Sn3akySqu1d/Squidboard/Images/image-20.png

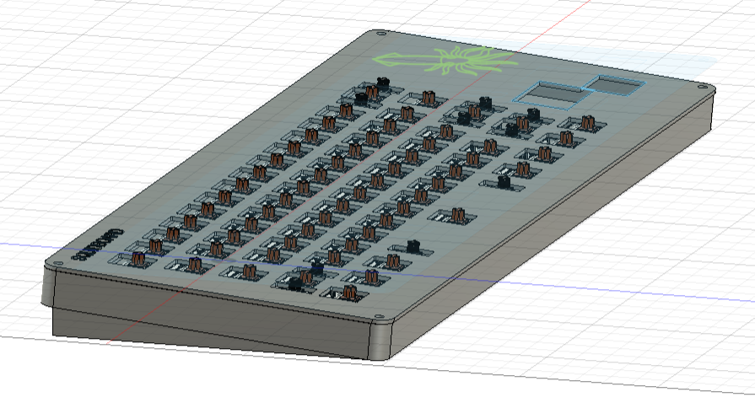
Images/image-20.png
