Sn3akySqu1d/Squidboard/Images/image.png

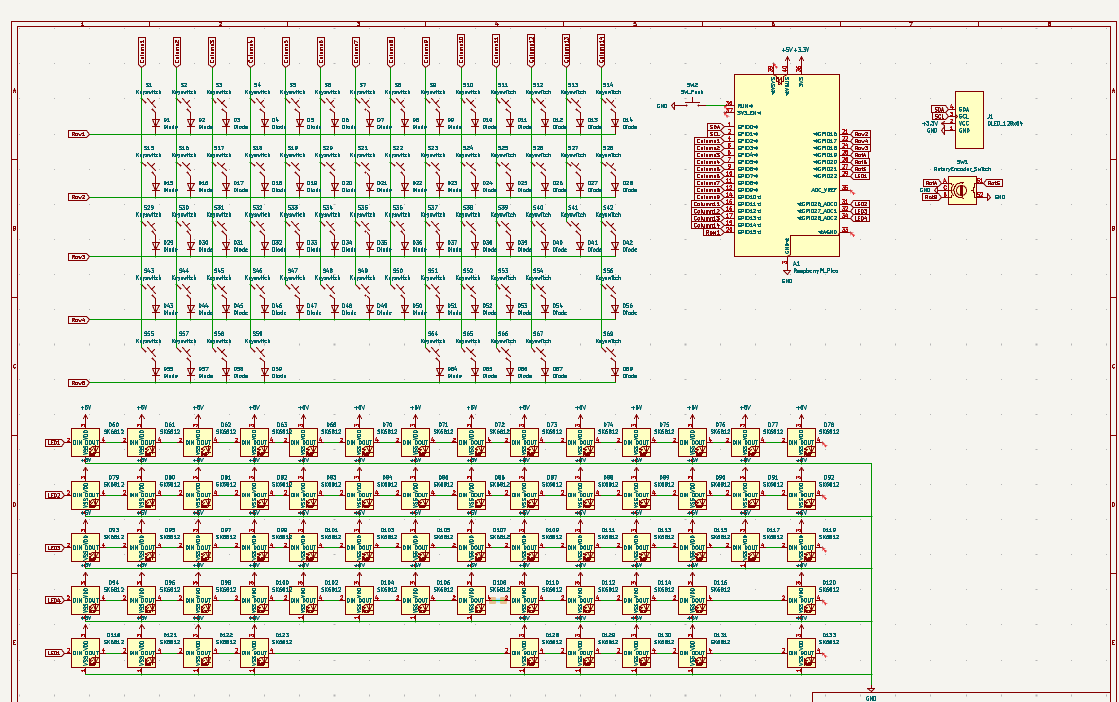
Images/image.png
