Sn3akySqu1d/Squidboard/JournalImages/image-1.png

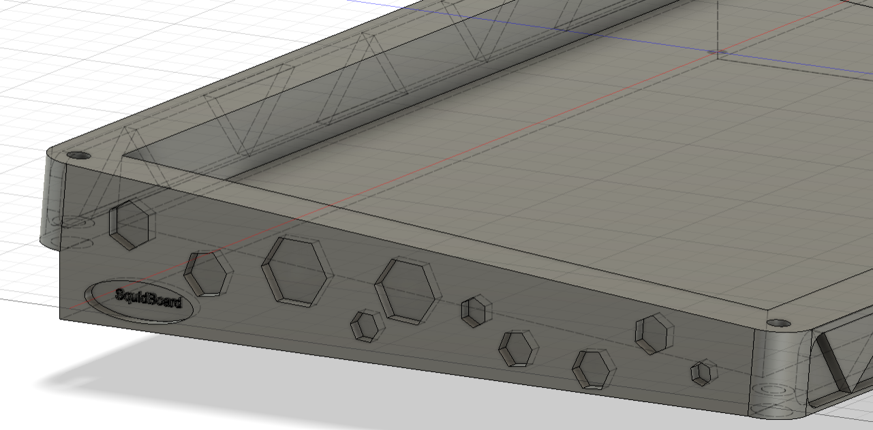
JournalImages/image-1.png
