Sn3akySqu1d/Squidboard/JournalImages/image-2.png

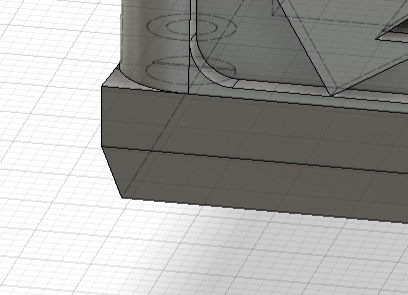
JournalImages/image-2.png
