Sn3akySqu1d/Squidboard/JournalImages/image-3.png

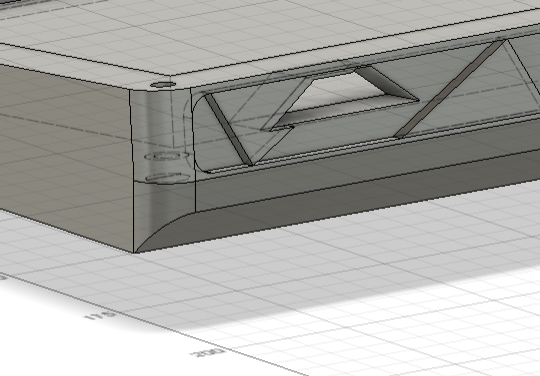
JournalImages/image-3.png
