Sn3akySqu1d/Squidboard/JournalImages/image-5.png

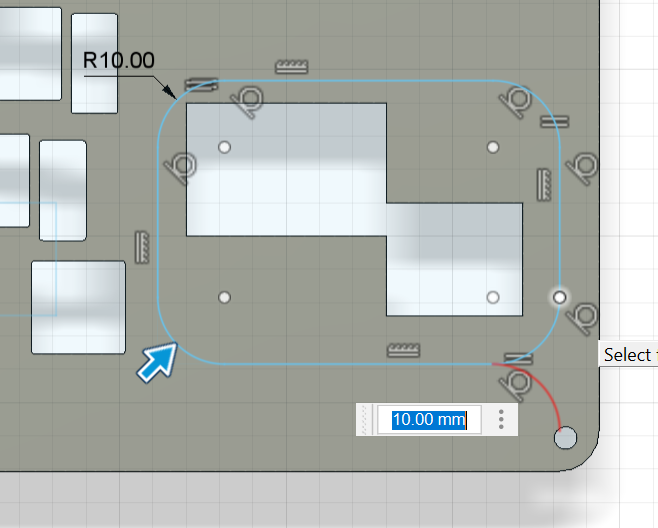
JournalImages/image-5.png
