Sn3akySqu1d/Squidboard/JournalImages/image-6.png

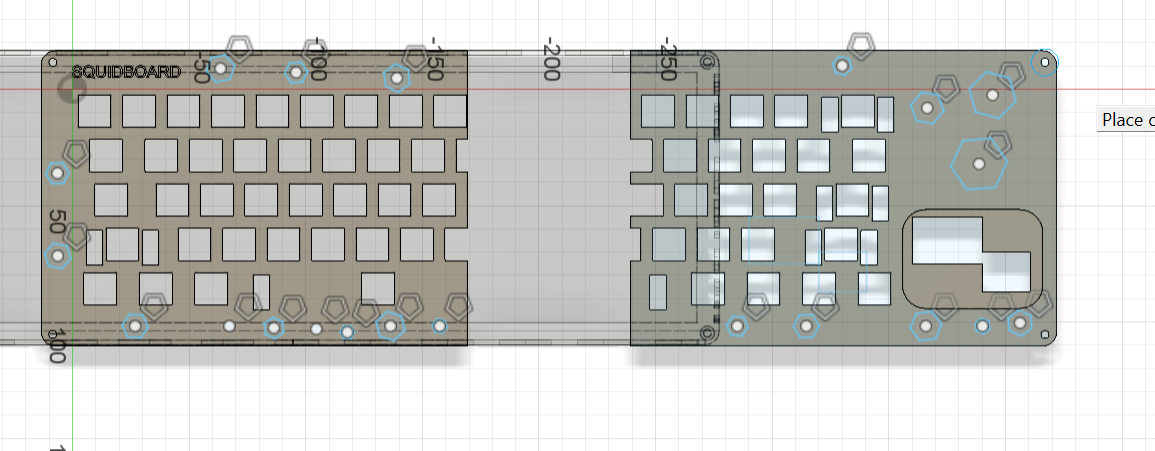
JournalImages/image-6.png
