Sn3akySqu1d/Squidboard/JournalImages/image-7.png

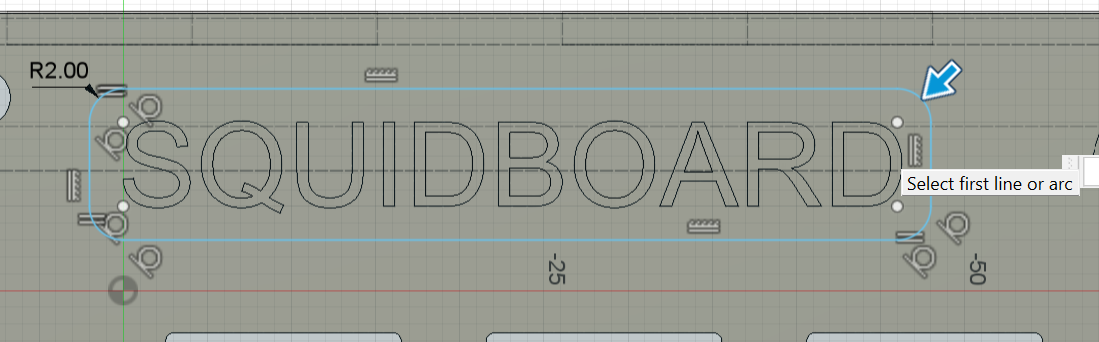
JournalImages/image-7.png
