Sn3akySqu1d/Squidboard/JournalImages/image-8.png

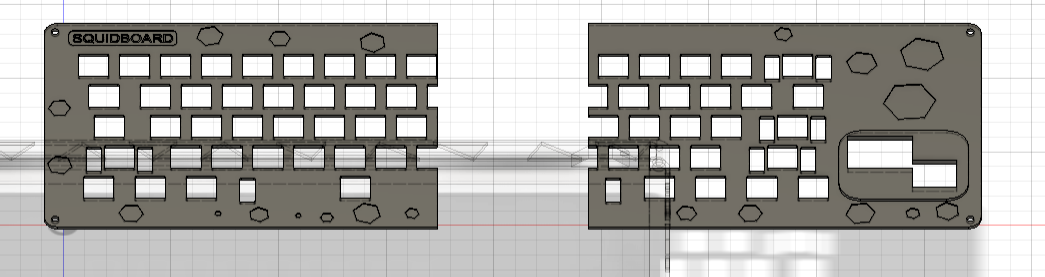
JournalImages/image-8.png
