Sn3akySqu1d/Squidboard/JournalImages/image-9.png

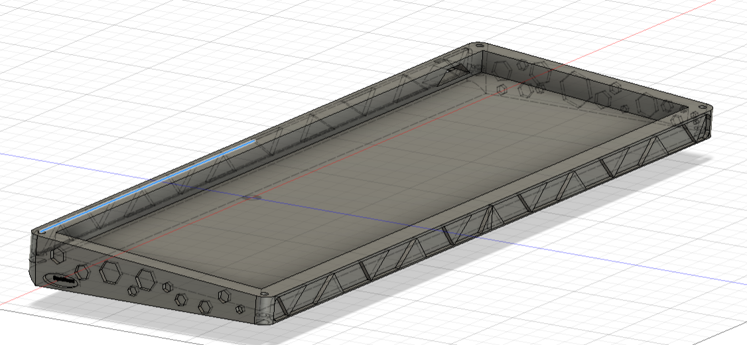
JournalImages/image-9.png
