Sn3akySqu1d/Squidboard/JournalImages/image-10.png

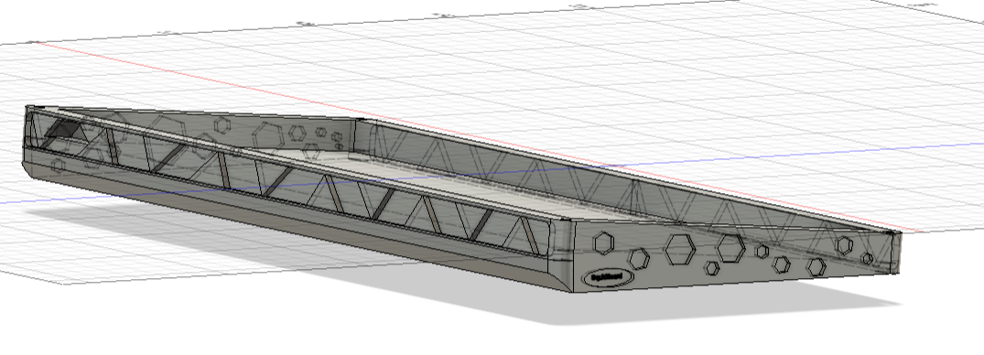
JournalImages/image-10.png
