Sn3akySqu1d/Squidboard/JournalImages/image-11.png

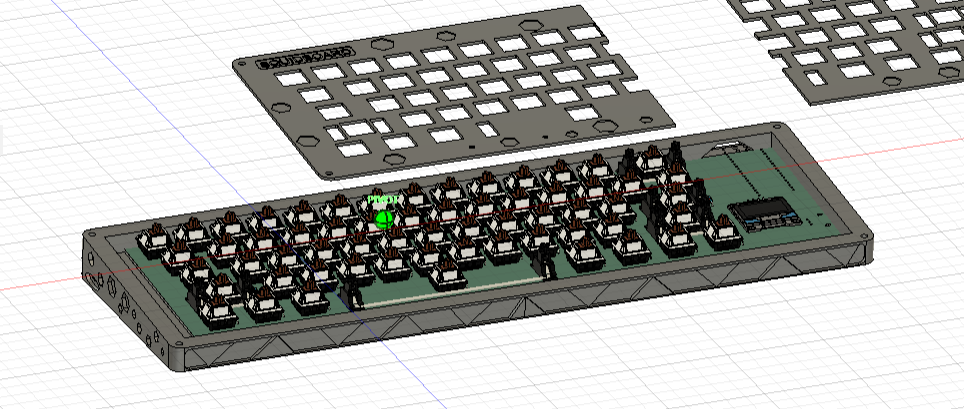
JournalImages/image-11.png
