Sn3akySqu1d/Squidboard/JournalImages/image-15.png

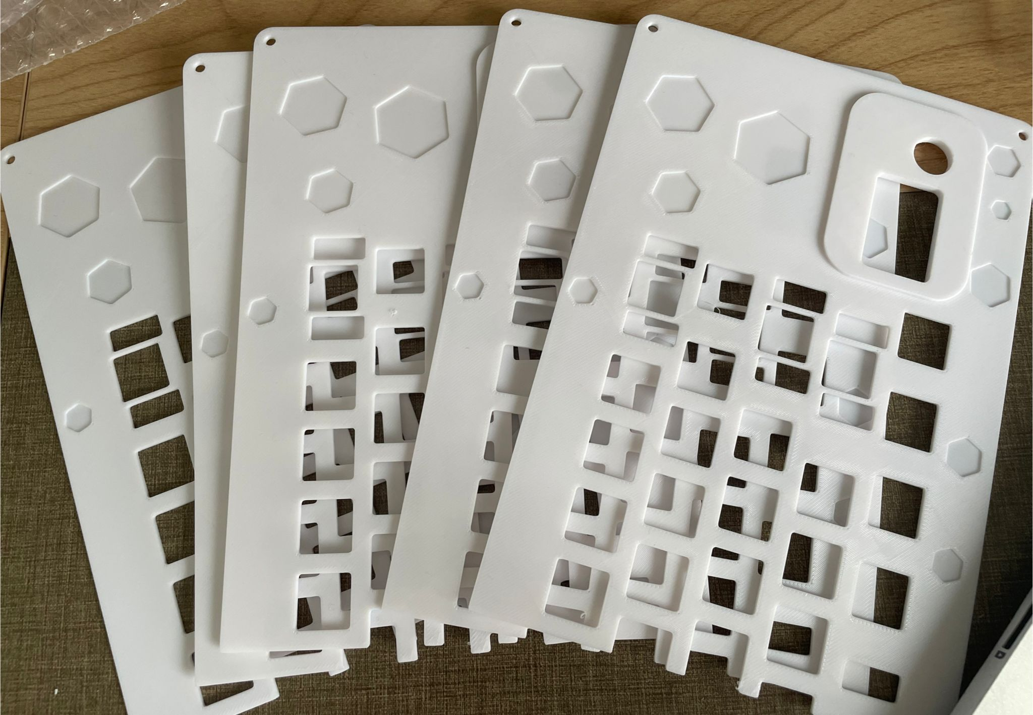
JournalImages/image-15.png
