Sn3akySqu1d/Squidboard/JournalImages/image-16.png

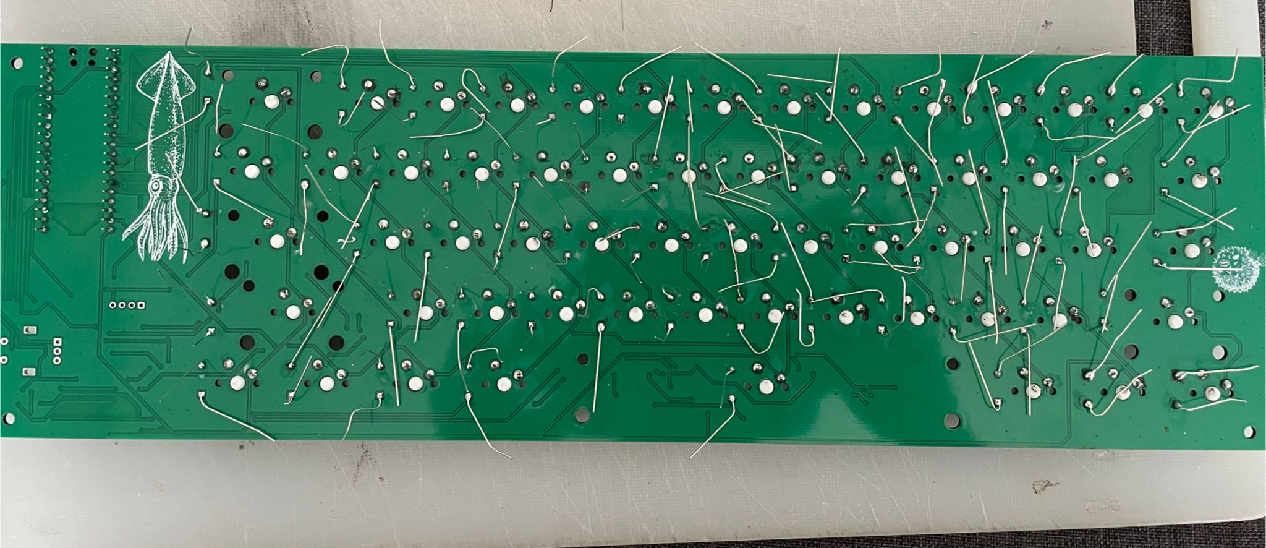
JournalImages/image-16.png
