Sn3akySqu1d/Squidboard/JournalImages/image-17.png

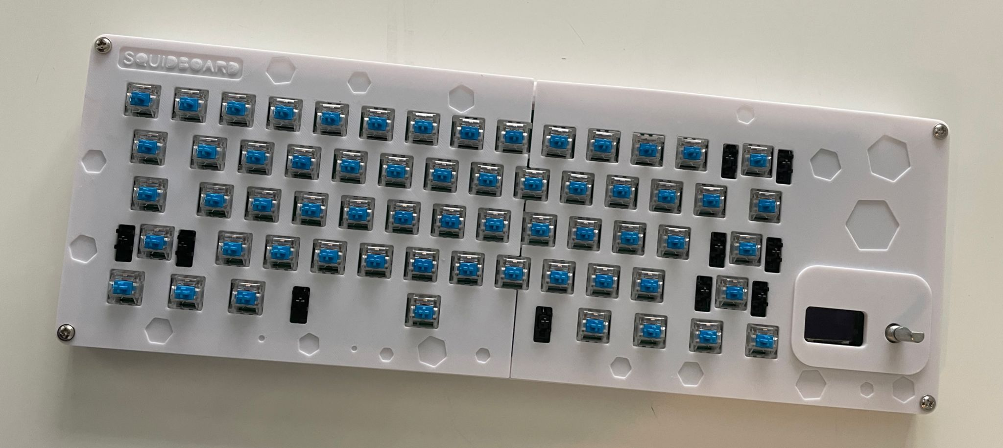
JournalImages/image-17.png
