Sn3akySqu1d/Squidboard/JournalImages/image-19.png

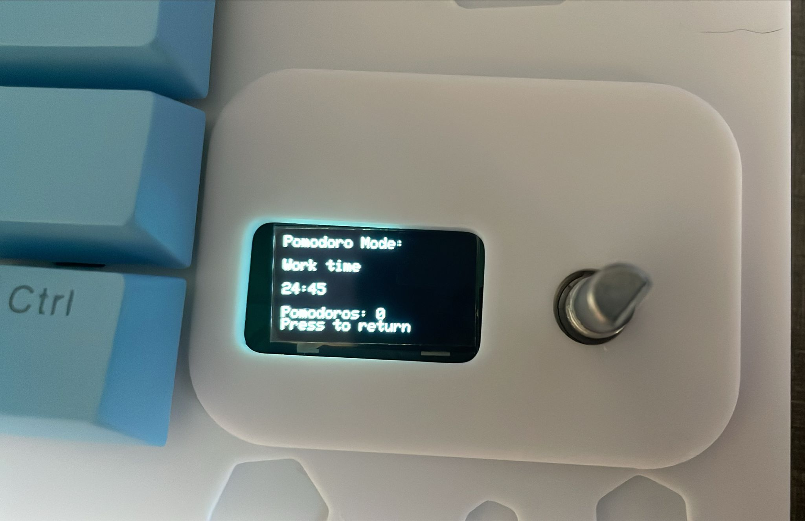
JournalImages/image-19.png
