Sn3akySqu1d/Squidboard/JournalImages/image.png

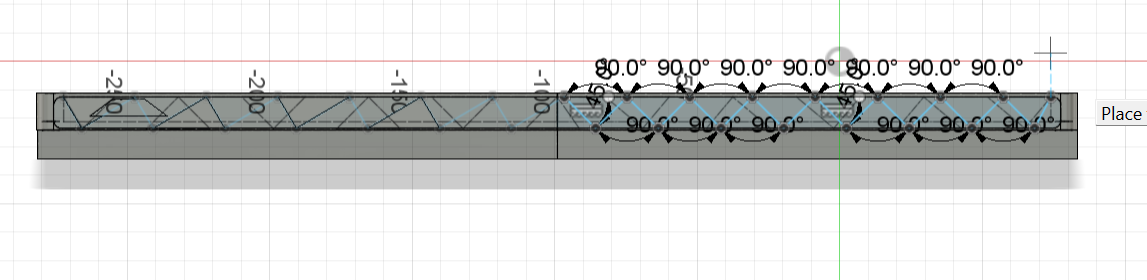
JournalImages/image.png
