Sn3akySqu1d/Squidboard/Kicad/Mechboard/Mechboard.kicad_sch

## KiCad design Kicad/Mechboard/Mechboard.kicad_sch (2025-07-20)

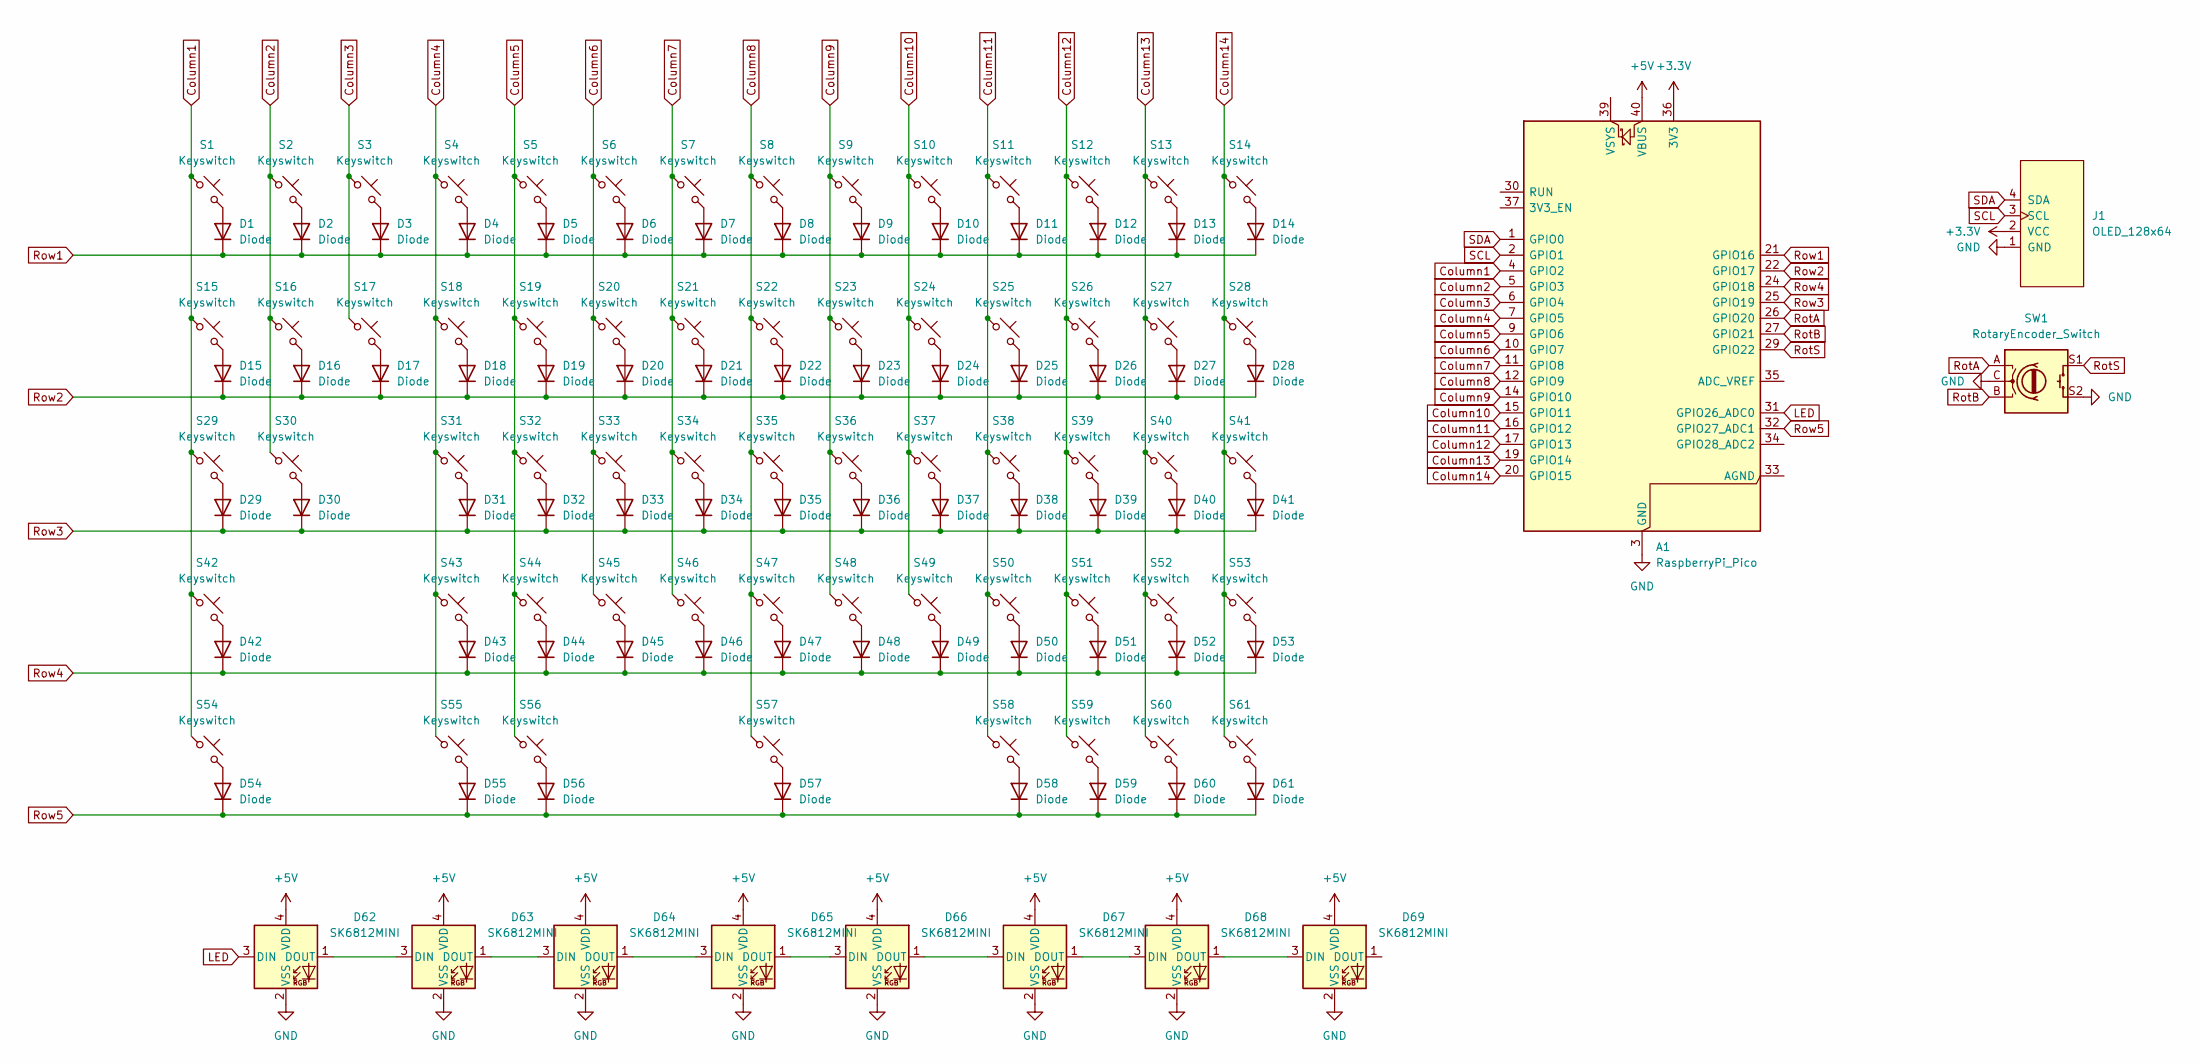
[picture p31: schematic Mechboard.kicad_sch]

Parts:
A1: RaspberryPi_Pico; RaspberryPi_Pico_Common_Unspecified
D1, D2, D3, D4, D5, D6, D7, D8, D9, D10, D11, D12, D13, D14, D15, D16, D17, D18, D19, D20, D21, D22, D23, D24, D25, D26, D27, D28, D29, D30, D31, D32, D33, D34, D35, D36, D37, D38, D39, D40, D41, D42, D43, D44, D45, D46, D47, D48, D49, D50, D51, D52, D53, D54, D55, D56, D57, D58, D59, D60, D61: Diode; Diode_DO-35
D62, D63, D64, D65, D66, D67, D68, D69: SK6812MINI; LED_SK6812MINI_PLCC4_3.5x3.5mm_P1.75mm
J1: OLED_128x64
S1, S2, S3, S4, S5, S6, S7, S8, S9, S10, S11, S12, S13, S16, S17, S18, S19, S20, S21, S22, S23, S24, S25, S26, S27, S30, S31, S32, S33, S34, S35, S36, S37, S38, S39, S40, S43, S44, S45, S46, S47, S48, S49, S50, S51, S52: Keyswitch; MX_PCB_1.00u
S14: Keyswitch; MX_PCB_2.00u
S15, S28: Keyswitch; MX_PCB_1.50u
S29: Keyswitch; MX_PCB_1.75u
S41, S42: Keyswitch; MX_PCB_2.25u
S53: Keyswitch; MX_PCB_2.75u
S54, S55, S56, S58, S59, S60, S61: Keyswitch; MX_PCB_1.25u
S57: Keyswitch; MX_PCB_6.25u
SW1: RotaryEncoder_Switch; RotaryEncoder_Alps_EC11E-Switch_Vertical_H20mm

Connections:
+3.3V: A1.36 (3V3), J1.2 (VCC)
+5V: A1.40 (VBUS), D62.4 (VDD), D63.4 (VDD), D64.4 (VDD), D65.4 (VDD), D66.4 (VDD), D67.4 (VDD), D68.4 (VDD), D69.4 (VDD)
Column1: A1.4 (GPIO2), S1.1, S15.1, S29.1, S42.1, S54.1
Column2: A1.5 (GPIO3), S2.1, S16.1, S30.1
Column3: A1.6 (GPIO4), S3.1, S17.1
Column4: A1.7 (GPIO5), S4.1, S18.1, S31.1, S43.1, S55.1
Column5: A1.9 (GPIO6), S5.1, S19.1, S32.1, S44.1, S56.1
Column6: A1.10 (GPIO7), S6.1, S20.1, S33.1, S45.1
Column7: A1.11 (GPIO8), S7.1, S21.1, S34.1, S46.1
Column8: A1.12 (GPIO9), S8.1, S22.1, S35.1, S47.1, S57.1
Column9: A1.14 (GPIO10), S9.1, S23.1, S36.1, S48.1
Column10: A1.15 (GPIO11), S10.1, S24.1, S37.1, S49.1
Column11: A1.16 (GPIO12), S11.1, S25.1, S38.1, S50.1, S58.1
Column12: A1.17 (GPIO13), S12.1, S26.1, S39.1, S51.1, S59.1
Column13: A1.19 (GPIO14), S13.1, S27.1, S40.1, S52.1, S60.1
Column14: A1.20 (GPIO15), S14.1, S28.1, S41.1, S53.1, S61.1
GND: A1.3 (GND), A1.8 (GND), A1.13 (GND), A1.18 (GND), A1.23 (GND), A1.28 (GND), A1.38 (GND), D62.2 (VSS), D63.2 (VSS), D64.2 (VSS), D65.2 (VSS), D66.2 (VSS), D67.2 (VSS), D68.2 (VSS), D69.2 (VSS), J1.1 (GND), SW1.C, SW1.S2
LED: A1.31 (GPIO26_ADC0), D62.3 (DIN)
unnamed: D1.2 (A), S1.2
unnamed: D2.2 (A), S2.2
unnamed: D3.2 (A), S3.2
unnamed: D4.2 (A), S4.2
unnamed: D5.2 (A), S5.2
unnamed: D6.2 (A), S6.2
unnamed: D7.2 (A), S7.2
unnamed: D8.2 (A), S8.2
unnamed: D9.2 (A), S9.2
unnamed: D10.2 (A), S10.2
unnamed: D11.2 (A), S11.2
unnamed: D12.2 (A), S12.2
unnamed: D13.2 (A), S13.2
unnamed: D14.2 (A), S14.2
unnamed: D15.2 (A), S15.2
unnamed: D16.2 (A), S16.2
unnamed: D17.2 (A), S17.2
unnamed: D18.2 (A), S18.2
unnamed: D19.2 (A), S19.2
unnamed: D20.2 (A), S20.2
unnamed: D21.2 (A), S21.2
unnamed: D22.2 (A), S22.2
unnamed: D23.2 (A), S23.2
unnamed: D24.2 (A), S24.2
unnamed: D25.2 (A), S25.2
unnamed: D26.2 (A), S26.2
unnamed: D27.2 (A), S27.2
unnamed: D28.2 (A), S28.2
unnamed: D29.2 (A), S29.2
unnamed: D30.2 (A), S30.2
unnamed: D31.2 (A), S31.2
unnamed: D32.2 (A), S32.2
unnamed: D33.2 (A), S33.2
unnamed: D34.2 (A), S34.2
unnamed: D35.2 (A), S35.2
unnamed: D36.2 (A), S36.2
unnamed: D37.2 (A), S37.2
unnamed: D38.2 (A), S38.2
unnamed: D39.2 (A), S39.2
unnamed: D40.2 (A), S40.2
unnamed: D41.2 (A), S41.2
unnamed: D42.2 (A), S42.2
unnamed: D43.2 (A), S43.2
unnamed: D44.2 (A), S44.2
unnamed: D45.2 (A), S45.2
unnamed: D46.2 (A), S46.2
unnamed: D47.2 (A), S47.2
unnamed: D48.2 (A), S48.2
unnamed: D49.2 (A), S49.2
unnamed: D50.2 (A), S50.2
unnamed: D51.2 (A), S51.2
unnamed: D52.2 (A), S52.2
unnamed: D53.2 (A), S53.2
unnamed: D54.2 (A), S54.2
unnamed: D55.2 (A), S55.2
unnamed: D56.2 (A), S56.2
unnamed: D57.2 (A), S57.2
unnamed: D58.2 (A), S58.2
unnamed: D59.2 (A), S59.2
unnamed: D60.2 (A), S60.2
unnamed: D61.2 (A), S61.2
unnamed: D62.1 (DOUT), D63.3 (DIN)
unnamed: D63.1 (DOUT), D64.3 (DIN)
unnamed: D64.1 (DOUT), D65.3 (DIN)
unnamed: D65.1 (DOUT), D66.3 (DIN)
unnamed: D66.1 (DOUT), D67.3 (DIN)
unnamed: D67.1 (DOUT), D68.3 (DIN)
unnamed: D68.1 (DOUT), D69.3 (DIN)
RotA: A1.26 (GPIO20), SW1.A
RotB: A1.27 (GPIO21), SW1.B
RotS: A1.29 (GPIO22), SW1.S1
Row1: A1.21 (GPIO16), D1.1 (K), D2.1 (K), D3.1 (K), D4.1 (K), D5.1 (K), D6.1 (K), D7.1 (K), D8.1 (K), D9.1 (K), D10.1 (K), D11.1 (K), D12.1 (K), D13.1 (K), D14.1 (K)
Row2: A1.22 (GPIO17), D15.1 (K), D16.1 (K), D17.1 (K), D18.1 (K), D19.1 (K), D20.1 (K), D21.1 (K), D22.1 (K), D23.1 (K), D24.1 (K), D25.1 (K), D26.1 (K), D27.1 (K), D28.1 (K)
Row3: A1.25 (GPIO19), D29.1 (K), D30.1 (K), D31.1 (K), D32.1 (K), D33.1 (K), D34.1 (K), D35.1 (K), D36.1 (K), D37.1 (K), D38.1 (K), D39.1 (K), D40.1 (K), D41.1 (K)
Row4: A1.24 (GPIO18), D42.1 (K), D43.1 (K), D44.1 (K), D45.1 (K), D46.1 (K), D47.1 (K), D48.1 (K), D49.1 (K), D50.1 (K), D51.1 (K), D52.1 (K), D53.1 (K)
Row5: A1.32 (GPIO27_ADC1), D54.1 (K), D55.1 (K), D56.1 (K), D57.1 (K), D58.1 (K), D59.1 (K), D60.1 (K), D61.1 (K)
SCL: A1.2 (GPIO1), J1.3 (SCL)
SDA: A1.1 (GPIO0), J1.4 (SDA)
